Chris-Johnston/ornament2022/pcb/ornament2022.kicad_sch

## KiCad design pcb/ornament2022.kicad_sch (2022-12-31)

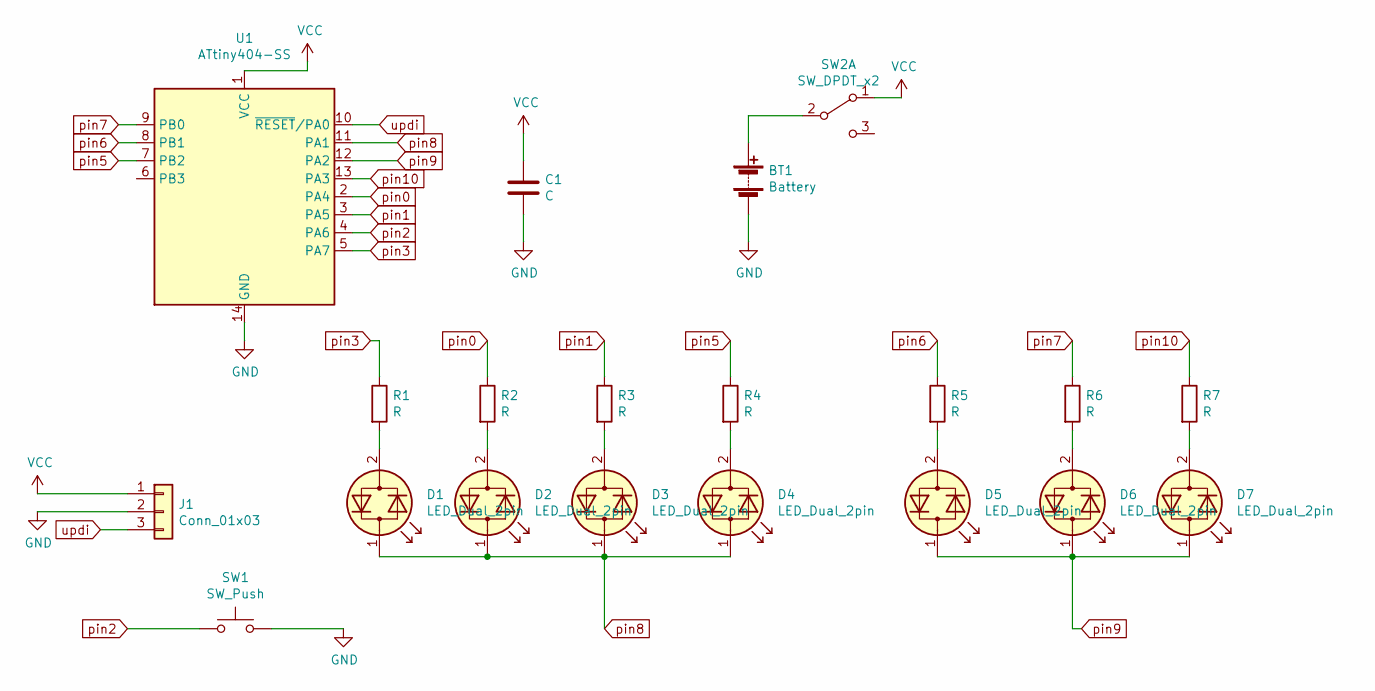
[picture p8: schematic ornament2022.kicad_sch]

Parts:
BT1: Battery; Custom_BatteryHolder_ComfortableElectronic_CH273-2450_1x2450
C1: C; C_1206_3216Metric_Pad1.42x1.75mm_HandSolder
D1, D2, D3, D4, D5, D6, D7: LED_Dual_2pin; Custom_LessSilkscreenLED_1206_3216Metric_Pad1.42x1.75mm_Han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
J1: Conn_01x03; custom_updipad_PinHeader_1x03_P2.54mm_Vertical
R1, R2, R3, R4, R5, R6, R7: R; R_1206_3216Metric_Pad1.42x1.75mm_HandSolder
SW1: SW_Push; SW_Push_1P1T_NO_6x6mm_H9.5mm
SW2: SW_DPDT_x2; SW_SPDT_CK-JS102011SAQN
U1: ATtiny404-SS; SOIC-14_3.9x8.7mm_P1.27mm

Connections:
GND: BT1.2 (-), C1.2, J1.2, SW1.2, U1.14 (GND)
unnamed: BT1.1 (+), SW2.2 (B)
unnamed: D1.2 (AK), R1.2
unnamed: D2.2 (AK), R2.2
unnamed: D3.2 (AK), R3.2
unnamed: D4.2 (AK), R4.2
unnamed: D5.2 (AK), R5.2
unnamed: D6.2 (AK), R6.2
unnamed: D7.2 (AK), R7.2
VCC: C1.1, J1.1, SW2.1 (A), U1.1 (VCC)
pin0: R2.1, U1.2 (PA4)
pin1: R3.1, U1.3 (PA5)
pin2: SW1.1, U1.4 (PA6)
pin3: R1.1, U1.5 (PA7)
pin5: R4.1, U1.7 (PB2)
pin6: R5.1, U1.8 (PB1)
pin7: R6.1, U1.9 (PB0)
pin8: D1.1 (KA), D2.1 (KA), D3.1 (KA), D4.1 (KA), U1.11 (PA1)
pin9: D5.1 (KA), D6.1 (KA), D7.1 (KA), U1.12 (PA2)
pin10: R7.1, U1.13 (PA3)
updi: J1.3, U1.10 (~RESET/PA0)
